MPrzekop/FV1-Craft-Store/Hardware/Drawings/LedTopDrawing.dxf

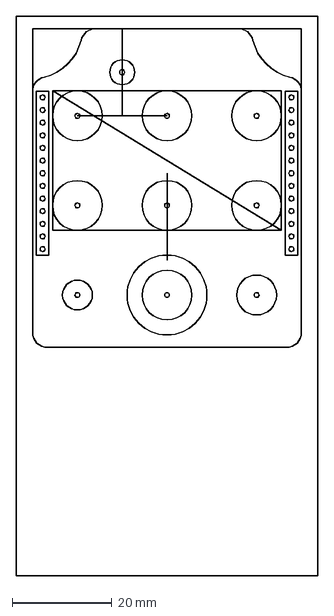
[picture p15: CAD file, 2025-02-01]
Hardware/Drawings/LedTopDrawing.dxf
60.5 x 112.4 mm
